siyouluo/RIRC_esp8266/ESP8266_Proj/images/esp8266_VirtualBox.png

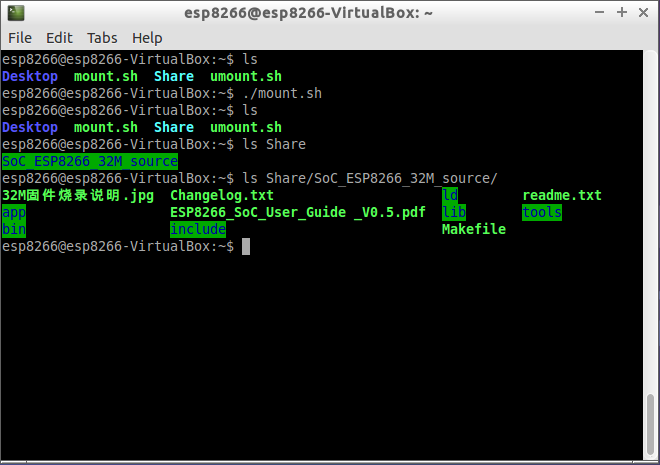
ESP8266_Proj/images/esp8266_VirtualBox.png
