siyouluo/RIRC_esp8266/Fritzing_Proj/images/breadboard.png

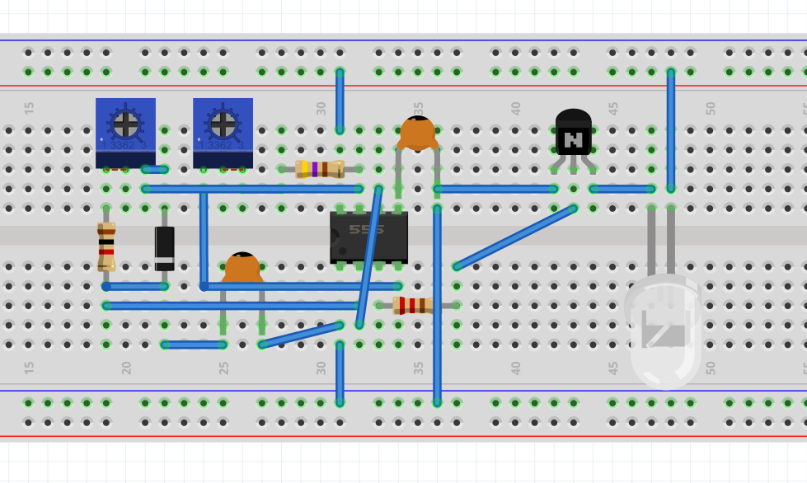
Fritzing_Proj/images/breadboard.png
