siyouluo/RIRC_esp8266/Fritzing_Proj/images/pcb.png

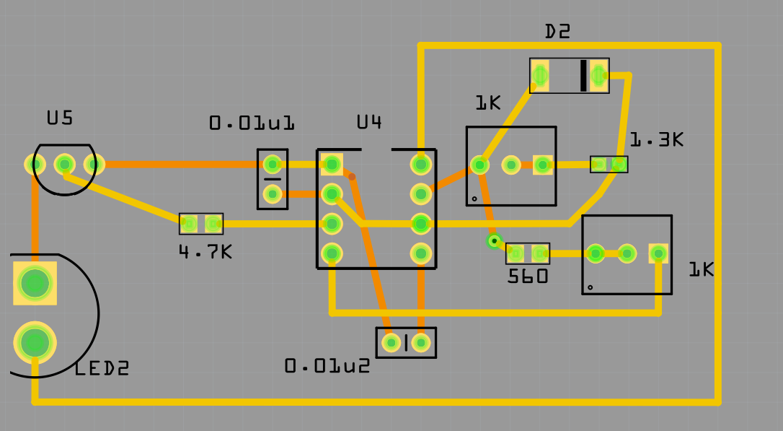
Fritzing_Proj/images/pcb.png
