siyouluo/RIRC_esp8266/Multisim_Proj/已调信号波形.png

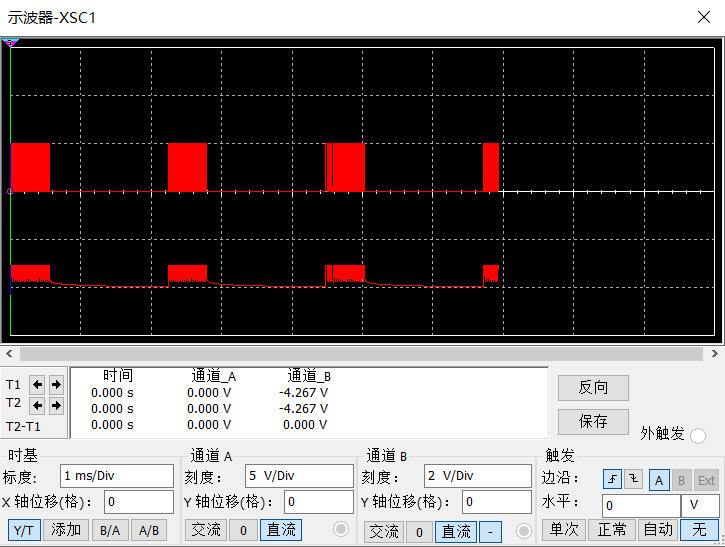
Multisim_Proj/已调信号波形.png
