siyouluo/RIRC_esp8266/Multisim_Proj/调制电路.png

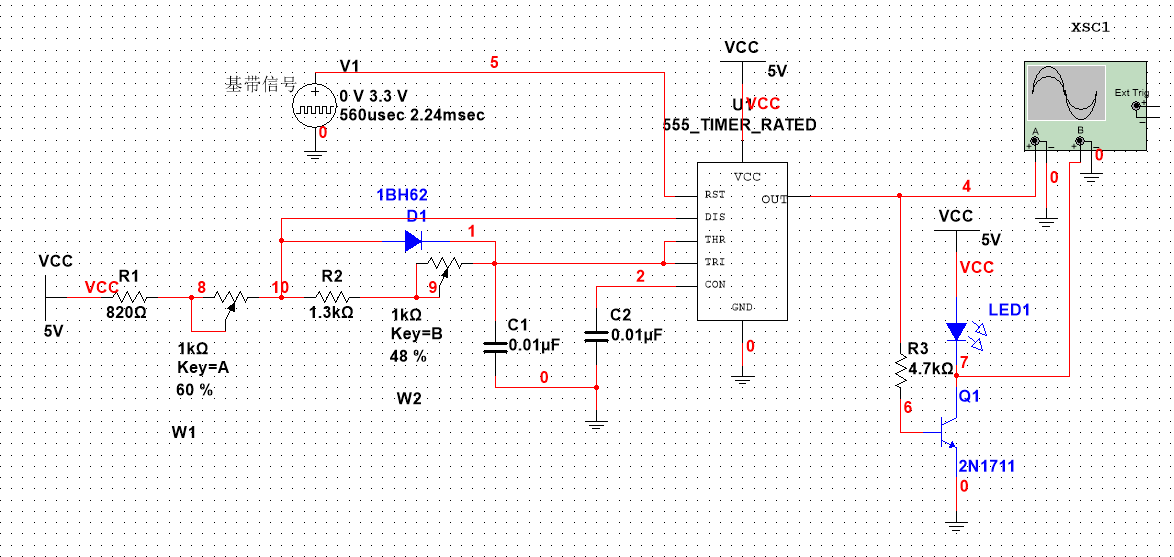
Multisim_Proj/调制电路.png
